PepVentura/SteamMachine-UM790/STL/Anagramas/Gung.stl

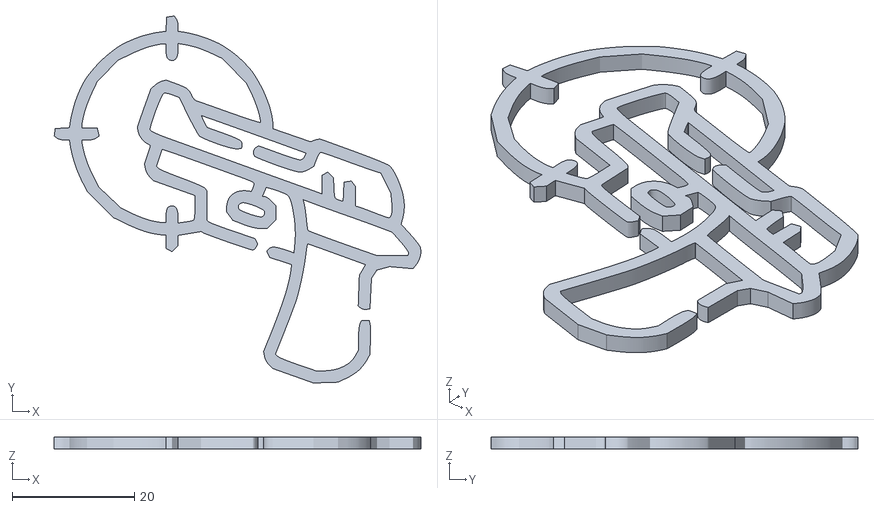
[picture p26: CAD file, 2026-08-29]
STL/Anagramas/Gung.stl
60.0 x 60.0 x 2.00
