PepVentura/SteamMachine-UM790/STL/caja_nfc_panel_caja_y_tapa.stl

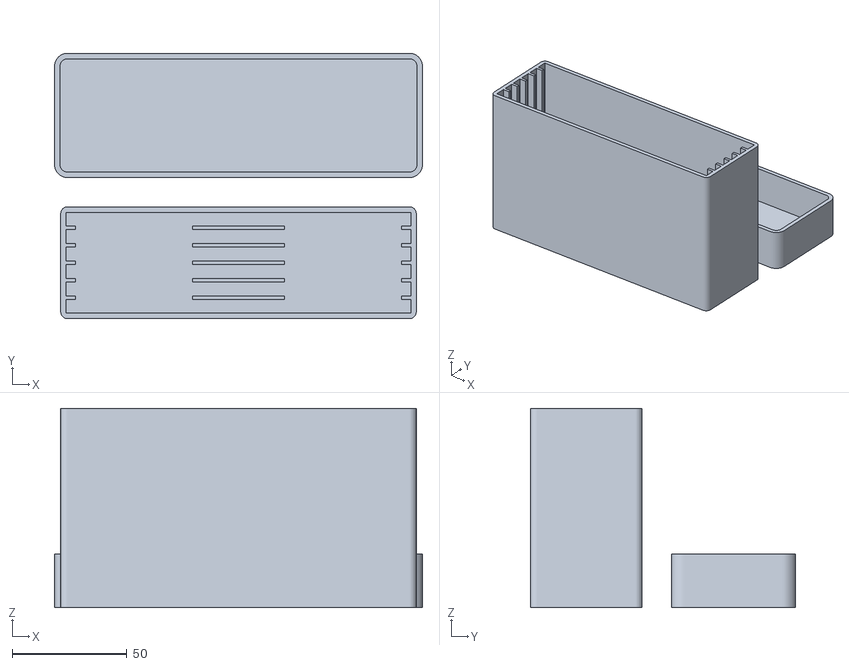
[picture p27: CAD file, 2026-09-24]
STL/caja_nfc_panel_caja_y_tapa.stl
160.4 x 115.7 x 86.9
