PepVentura/SteamMachine-UM790/STL/Anagramas/Retrobat.stl

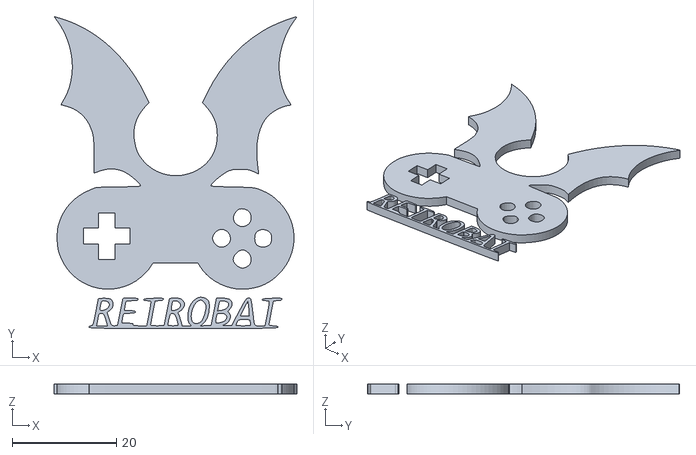
[picture p28: CAD file, 2026-08-29]
STL/Anagramas/Retrobat.stl
46.6 x 60.0 x 2.00
