PepVentura/SteamMachine-UM790/STL/Anagramas/nfc_panel_blank.stl

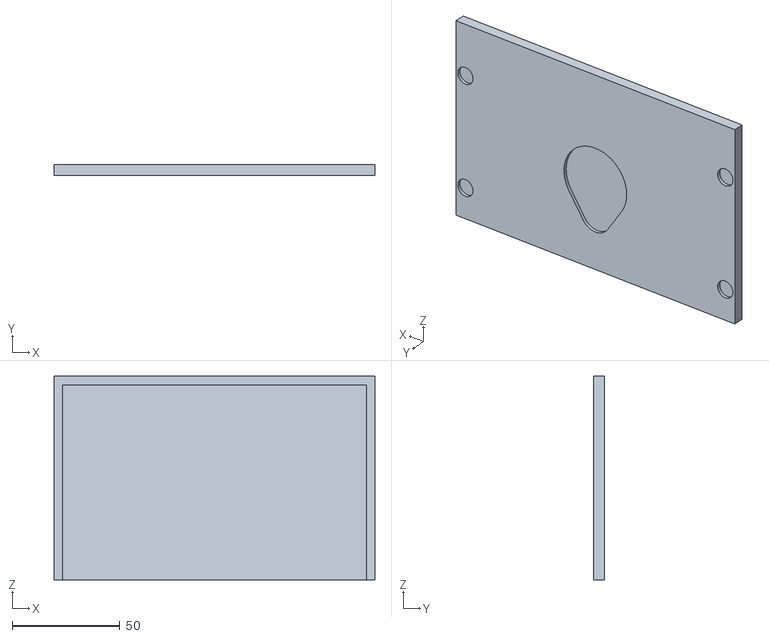
[picture p29: CAD file, 2026-08-19]
STL/Anagramas/nfc_panel_blank.stl
149.0 x 5.00 x 94.5
