PepVentura/SteamMachine-UM790/STL/rc522_bracket2.stl

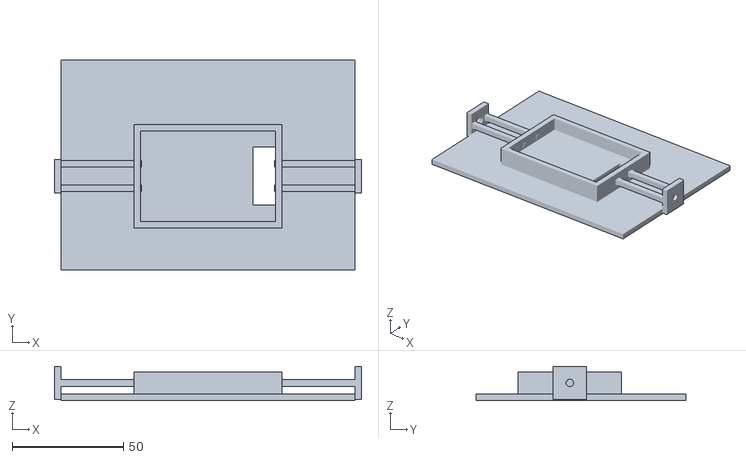
[picture p30: CAD file, 2026-09-08]
STL/rc522_bracket2.stl
138.0 x 94.5 x 15.5
