PepVentura/SteamMachine-UM790/STL/foot.stl

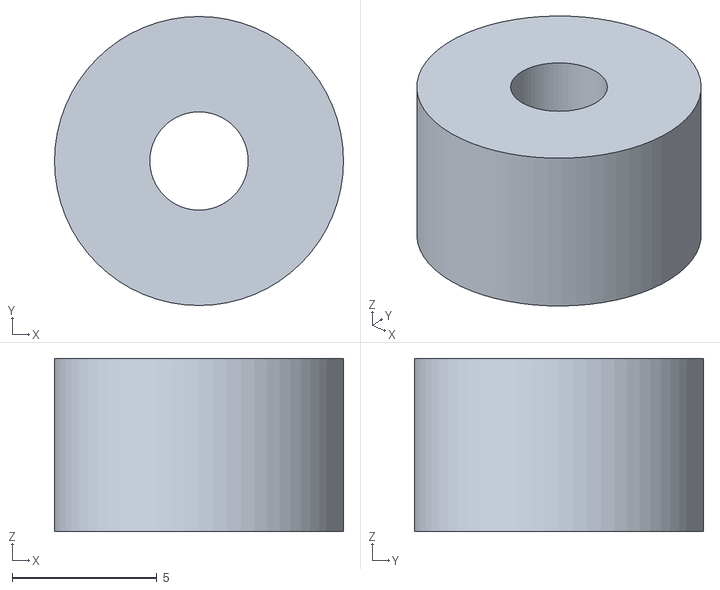
[picture p31: CAD file, 2026-09-03]
STL/foot.stl
10.0 x 10.0 x 6.00
