PepVentura/SteamMachine-UM790/STL/rear_panel.stl

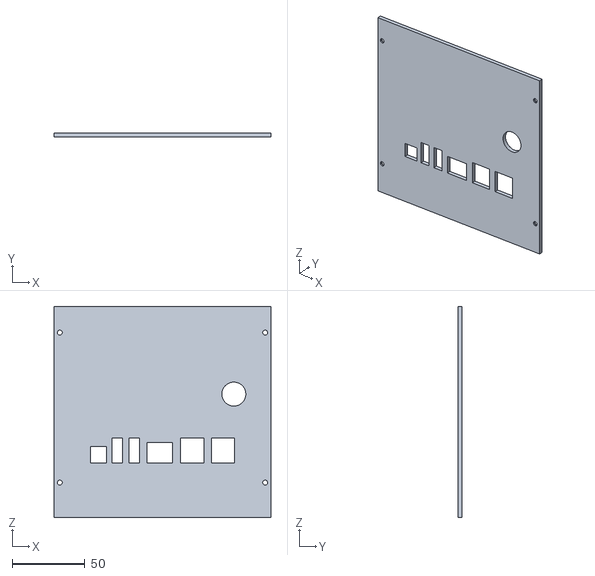
[picture p32: CAD file, 2026-08-30]
STL/rear_panel.stl
149.0 x 3.00 x 145.0
