PepVentura/SteamMachine-UM790/STL/top.stl

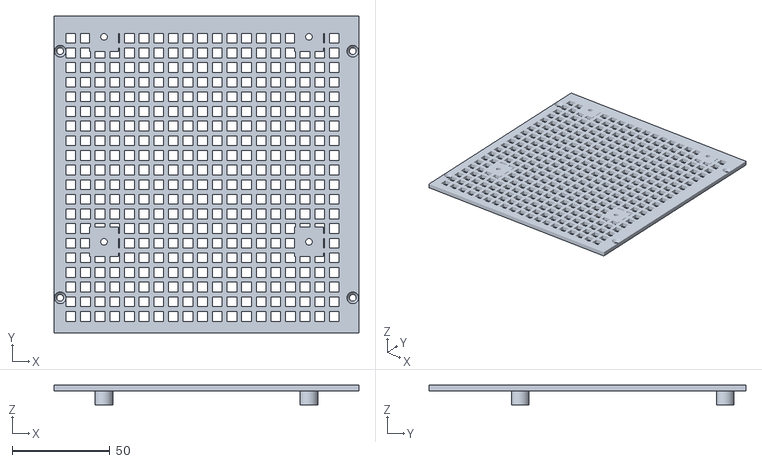
[picture p33: CAD file, 2026-08-29]
STL/top.stl
156.0 x 162.4 x 10.0
