PepVentura/SteamMachine-UM790/STL/tray.stl

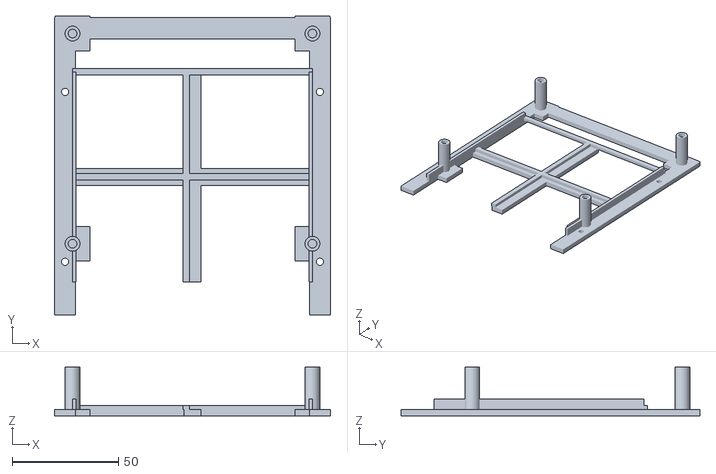
[picture p34: CAD file, 2026-08-29]
STL/tray.stl
130.0 x 140.7 x 23.0
