PepVentura/SteamMachine-UM790/STL/lower_panel.stl

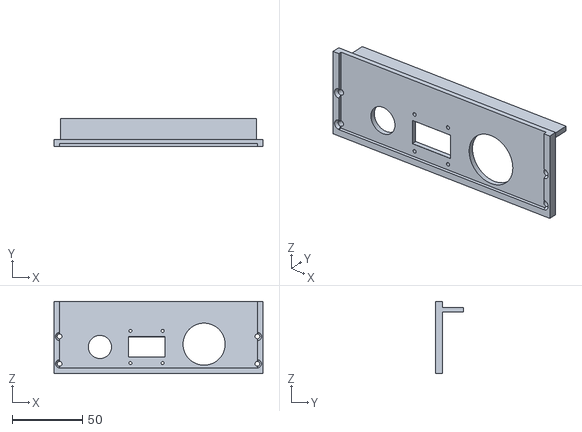
[picture p35: CAD file, 2026-08-29]
STL/lower_panel.stl
149.0 x 20.0 x 51.5
