PepVentura/SteamMachine-UM790/STL/chassis.stl

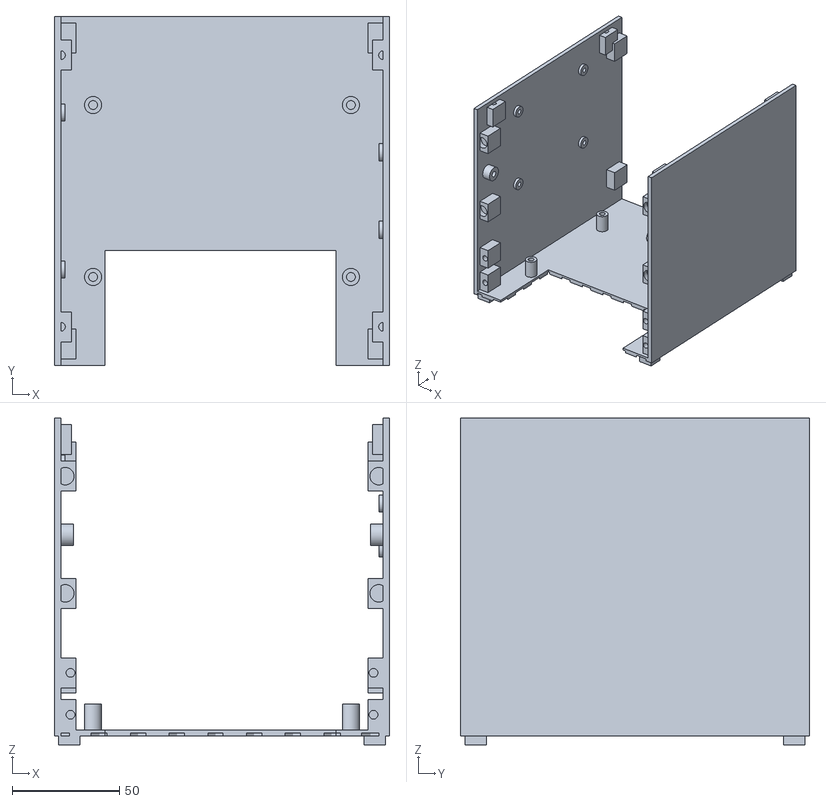
[picture p36: CAD file, 2026-08-29]
STL/chassis.stl
156.0 x 162.4 x 152.0
