PepVentura/SteamMachine-UM790/STL/floor.stl

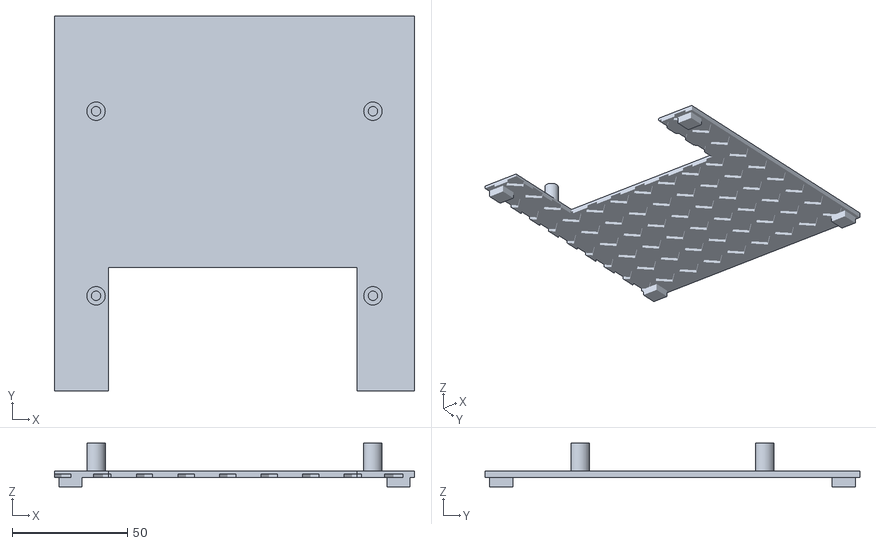
[picture p37: CAD file, 2026-08-29]
STL/floor.stl
156.0 x 162.4 x 19.0
