PepVentura/SteamMachine-UM790/STL/rc522_bracket.stl

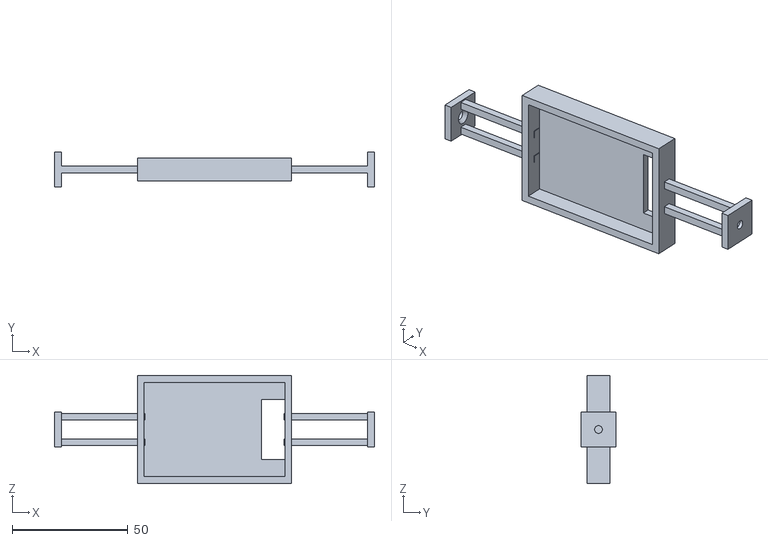
[picture p38: CAD file, 2026-08-29]
STL/rc522_bracket.stl
138.0 x 15.0 x 46.6
