PepVentura/SteamMachine-UM790/openscad/parts/02_chassis/chassis_lower.scad

//
// ============================================================================
// SteamMachine UM790
// Project Phoenix
//
// Archivo : chassis_lower.scad
// Versión : 2.0
//
// Chasis inferior
//
// Bloque 1:
// - Fondo
// - Pared izquierda
// - Pared derecha
// - Pared frontal
//
// ⚠️ OBSOLETO (2026-08-03) — sustituido por, en la misma carpeta:
//   - floor.scad (suelo, con rejilla y apoyos de la bandeja)
//   - walls.scad (paredes laterales, con imanes y anclajes)
//   - top.scad (tapa, no existía en este archivo)
//   - chassis.scad (ensamblado de las tres piezas anteriores)
//
// Este archivo incluía una PARED FRONTAL fija que ya no corresponde
// al diseño confirmado (el panel frontal es magnético y desmontable,
// sin pared fija detrás — ver docs/Virtual_Assembly_Report.md).
// Se conserva sin borrar como referencia histórica, pero no debe
// usarse para imprimir.
//
// ============================================================================

include <../../../00_parametros.scad>;

$fn = 64;


//=============================================================================
// PARÁMETROS
//=============================================================================

air_gap = 12;


//=============================================================================
// FONDO
//=============================================================================

module chassis_floor()
{

    cube(
    [
        case_width,
        case_depth,
        bottom_thickness
    ]);

}


//=============================================================================
// PARED IZQUIERDA
//=============================================================================

module left_wall()
{

    cube(
    [
        wall_thickness,
        case_depth,
        case_height
    ]);

}


//=============================================================================
// PARED DERECHA
//=============================================================================

module right_wall()
{

    translate(
    [
        case_width-wall_thickness,
        0,
        0
    ])

    cube(
    [
        wall_thickness,
        case_depth,
        case_height
    ]);

}


//=============================================================================
// PARED FRONTAL
//=============================================================================

module front_wall()
{

    cube(
    [
        case_width,
        wall_thickness,
        case_height
    ]);

}


//=============================================================================
// CHASIS
//=============================================================================

module chassis_lower()
{

    union()
    {

        chassis_floor();

        left_wall();

        right_wall();

        front_wall();

    }

}


//=============================================================================
// PREVIEW
//=============================================================================

translate(
[
    -case_width/2,
    -case_depth/2,
    0
])

color("Gainsboro")
    chassis_lower();
