PepVentura/SteamMachine-UM790/openscad/parts/Caja paneles NFC/caja_nfc_panel.scad

// =====================================================================
//  Caja con guías internas y tapa para 6 paneles "nfc_panel_blank"
//  Medidas de la pieza (extraídas del STL): 149 x 94.5 x 5 mm
//    ancho (X) = 149   alto (Z) = 94.5   grosor (Y) = 5
//
//  Las piezas se guardan de canto (de pie), una detrás de otra,
//  cada una en su ranura. Sobresalen por arriba para poder cogerlas
//  y la tapa es una "funda" que se desliza por fuera de la caja.
//
//  Material: PETG (ver docs/14_Caja_Paneles_NFC.md). Si la tapa queda
//  dura, sube lid_clr a 0.4.
//  Impresión (sin soportes):
//    - Caja: base apoyada en la cama.
//    - Tapa: se imprime boca abajo (ya viene girada en part="print").
// =====================================================================

/* [Qué mostrar] */
// print = caja + tapa listas para imprimir | box | lid | assembly = montada
part = "print";   // [print, box, lid, assembly]
// Muestra las piezas de ejemplo (bloques) dentro de la caja
show_pieces = true;

/* [Pieza a guardar] */
piece_w = 149;    // ancho (X)
piece_h = 94.5;   // alto (Z)
piece_t = 5;      // grosor (Y)
n_pieces = 6;     // número de piezas

/* [Holguras] */
clr_x = 0.6;      // holgura lateral por lado
clr_t = 1.0;      // holgura extra en cada ranura (grosor)
lid_clr = 0.3;    // holgura tapa/caja por lado (sube a 0.4 si queda dura)
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
